performantp/radiation_pattern_drone/RX_SI4735_30_TFT_ST7735_SHARE_JCR_REV_2_1/Install these libraries/Rotary-master/Rotary.h

/*
 * Rotary encoder library for Arduino.
 */

#ifndef Rotary_h
#define Rotary_h

#include "Arduino.h"

// Enable this to emit codes twice per step. JCR: DOBRA VELOCIDADE DO ENC. ORIG IS DISABLED
#define HALF_STEP

// Enable weak pullups
#define ENABLE_PULLUPS

// Values returned by 'process'
// No complete step yet.
#define DIR_NONE 0x0
// Clockwise step.
#define DIR_CW 0x10
// Counter-clockwise step.
#define DIR_CCW 0x20

class Rotary
{
  public:
    Rotary(char, char);
    unsigned char process();
  private:
    unsigned char state;
    unsigned char pin1;
    unsigned char pin2;
};

#endif
 
